danielmader/LEDclock_DCF77-RTC_MicroPythonESP/src/characters.py

## Kompakte 3x5-Schrift (Zeichenbreite 3 px + 1 px Abstand)
FONT_3X5 = {
    "_meta_": {"width": 3, "height": 5},
    " ": (
        0b000,
        0b000,
        0b000,
        0b000,
        0b000,
        ),
    "!": (
        0b010,
        0b010,
        0b010,
        0b000,
        0b010,
        ),
    ":": (
        0b000,
        0b010,
        0b000,
        0b010,
        0b000,
        ),
    ",": (
        0b000,
        0b000,
        0b000,
        0b010,
        0b100,
        ),
    ".": (
        0b000,
        0b000,
        0b000,
        0b000,
        0b010,
        ),
    "°": (
        0b010,
        0b101,
        0b010,
        0b000,
        0b000,
        ),
    "%": (
        0b101,
        0b001,
        0b010,
        0b100,
        0b101,
        ),
    "-": (
        0b000,
        0b000,
        0b111,
        0b000,
        0b000,
        ),
    "_": (
        0b000,
        0b000,
        0b000,
        0b000,
        0b111,
        ),
    "#": (
        0b101,
        0b111,
        0b101,
        0b111,
        0b101,
        ),
    "+": (
        0b000,
        0b010,
        0b111,
        0b010,
        0b000,
        ),
    "*": (
        0b101,
        0b010,
        0b111,
        0b010,
        0b101,
        ),
    "/": (
        0b001,
        0b001,
        0b010,
        0b100,
        0b100,
        ),
    "|": (
        0b010,
        0b010,
        0b010,
        0b010,
        0b010,
        ),
    "=": (
        0b000,
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
    ),
    " ": (
        0b00000,
        0b00000,
        0b00000,
        0b00000,
        0b00000,
        0b00000,
        0b00000,
    ),
    "&": (
        0b01100,
        0b10010,
        0b10100,
        0b01000,
        0b10101,
        0b10010,
        0b01101,
    ),
}
